Tobias-Huth/BinClock/pics/20241218_153026.jpg

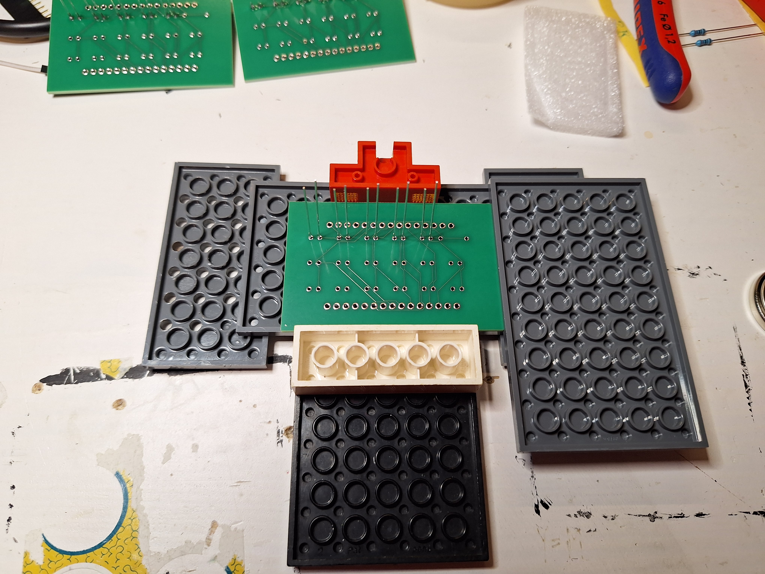
pics/20241218_153026.jpg
