Tobias-Huth/BinClock/pics/20241218_160921.jpg

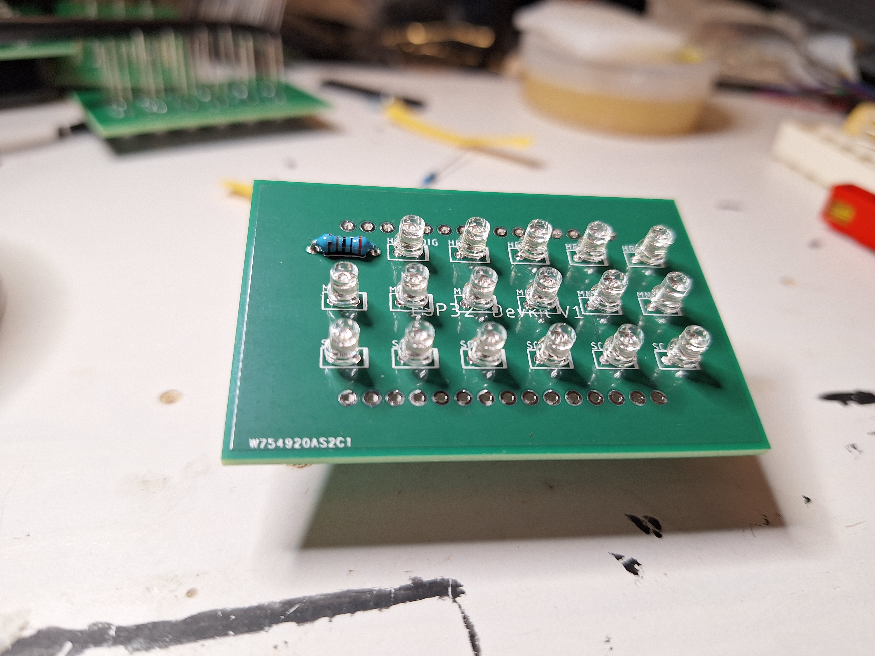
pics/20241218_160921.jpg
