Tobias-Huth/BinClock/pics/20241218_161102.jpg

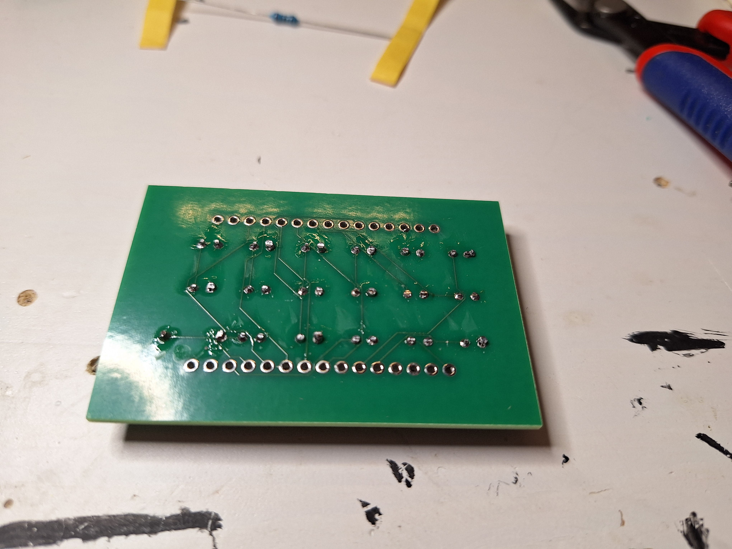
pics/20241218_161102.jpg
