Tobias-Huth/BinClock/pics/20241218_162006.jpg

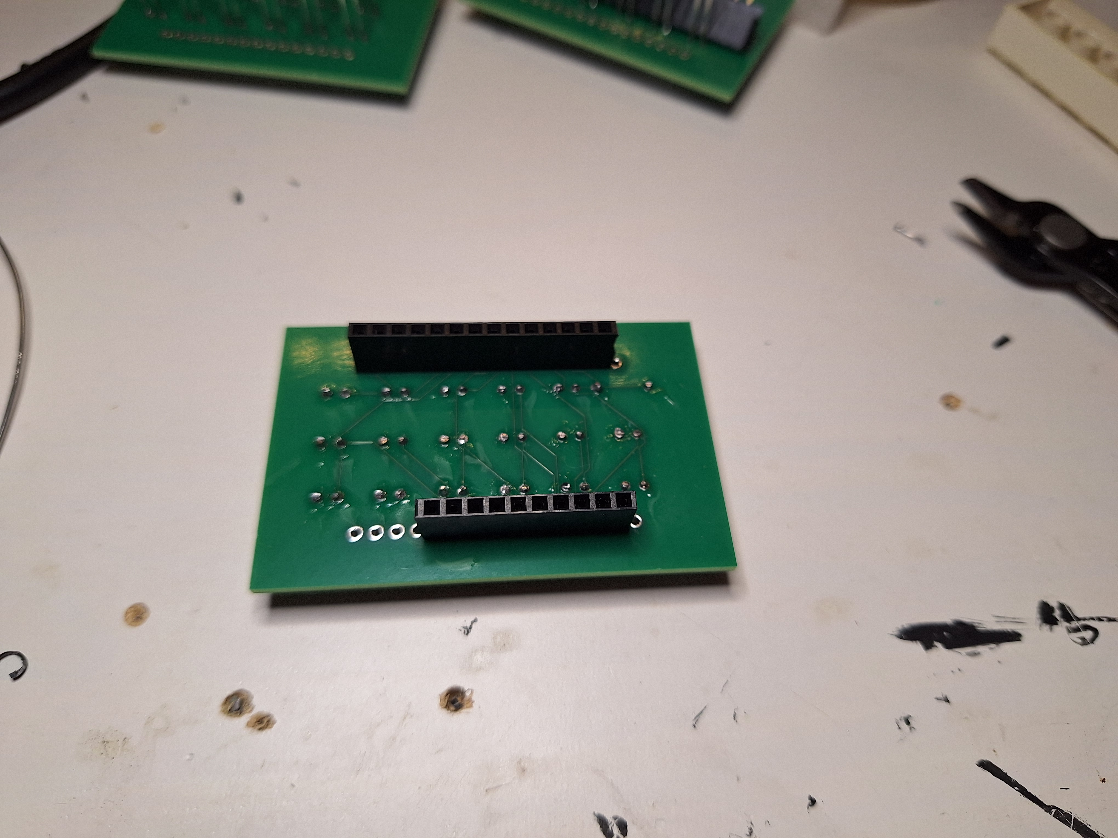
pics/20241218_162006.jpg
