Tobias-Huth/BinClock/pics/20241219_142211.jpg

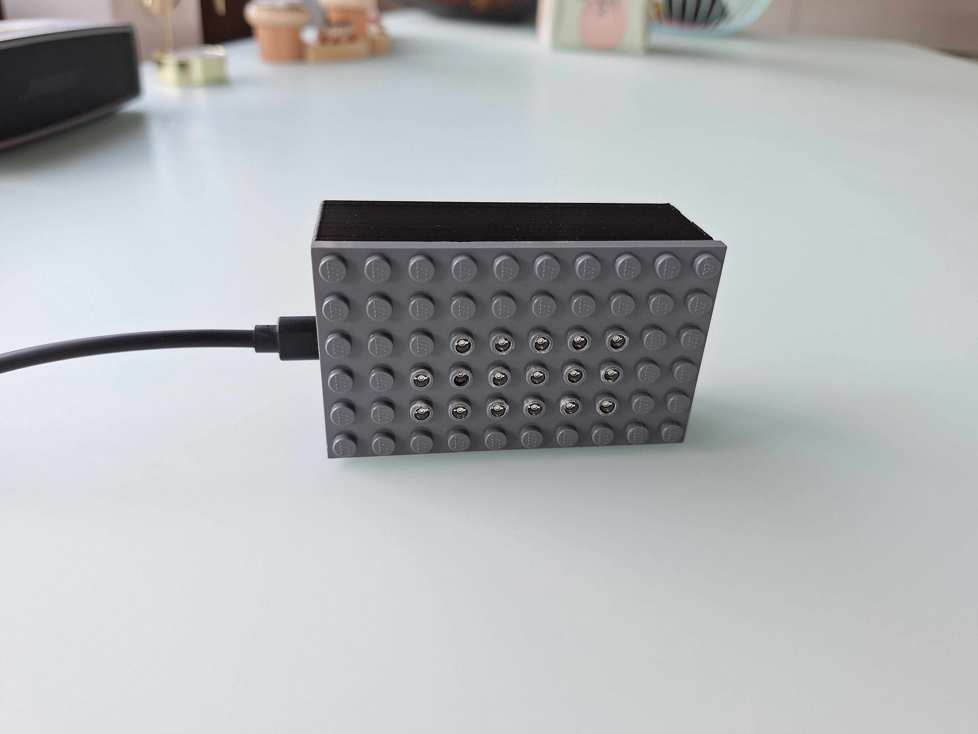
pics/20241219_142211.jpg
