Tobias-Huth/BinClock/pics/20241219_142215.jpg

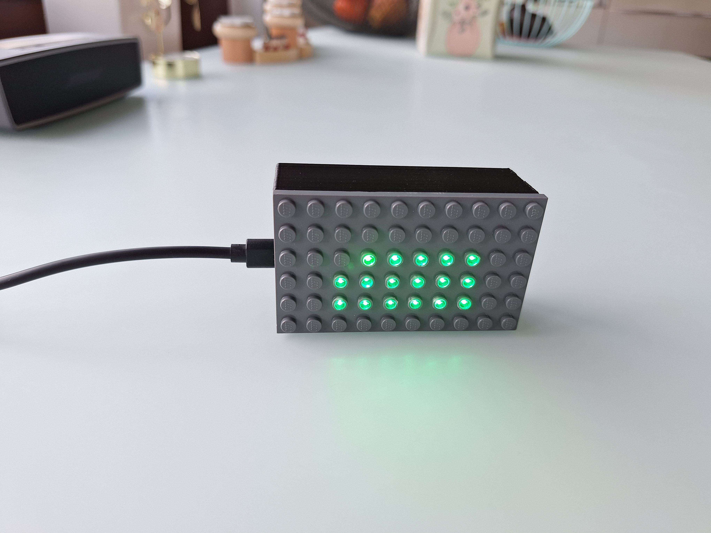
pics/20241219_142215.jpg
