Tobias-Huth/BinClock/pics/20241219_142327.jpg

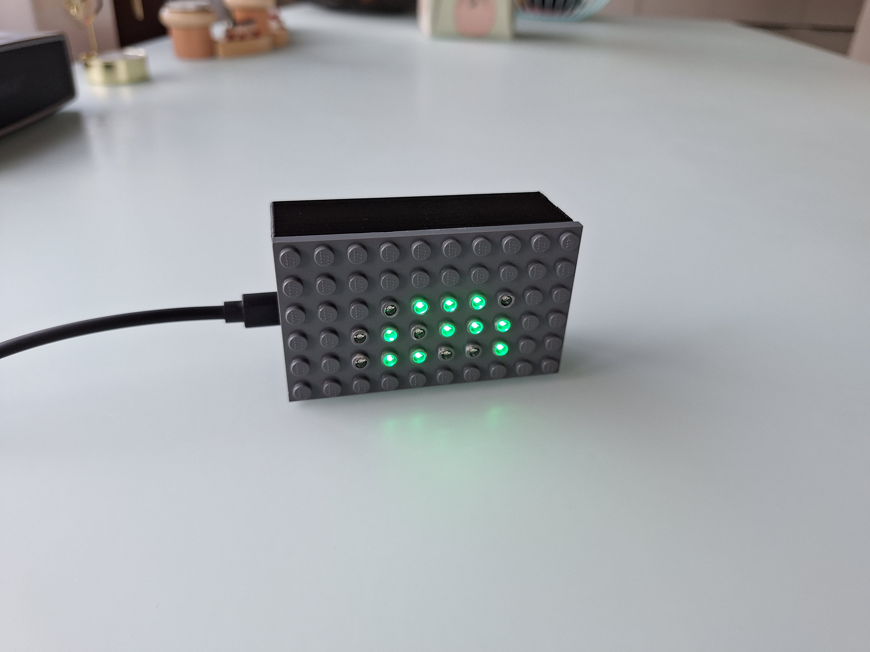
pics/20241219_142327.jpg
