Tobias-Huth/BinClock/pics/20241219_142519.jpg

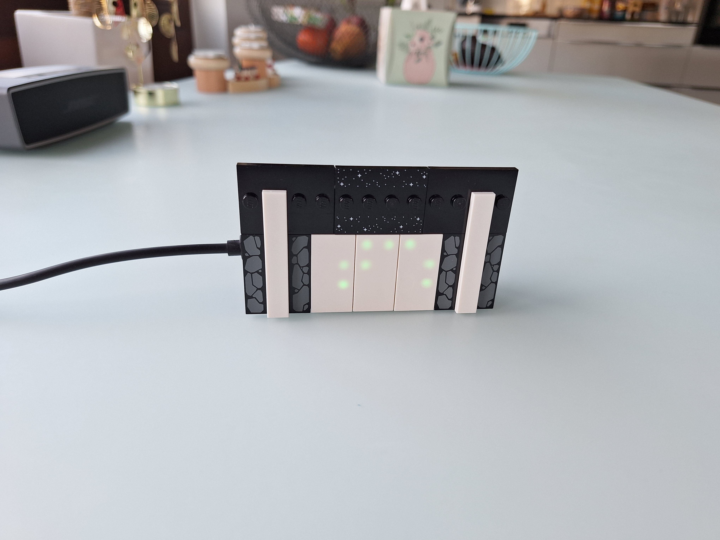
pics/20241219_142519.jpg
