Tobias-Huth/BinClock/pics/20241219_144131.jpg

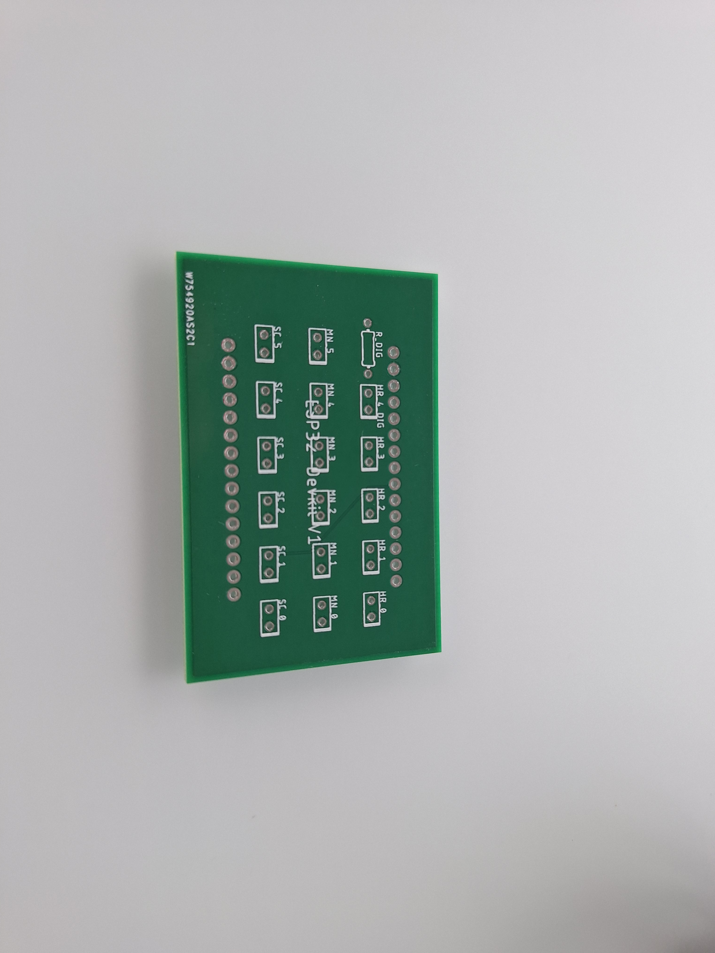
pics/20241219_144131.jpg
