Tobias-Huth/BinClock/pics/20241219_145637.jpg

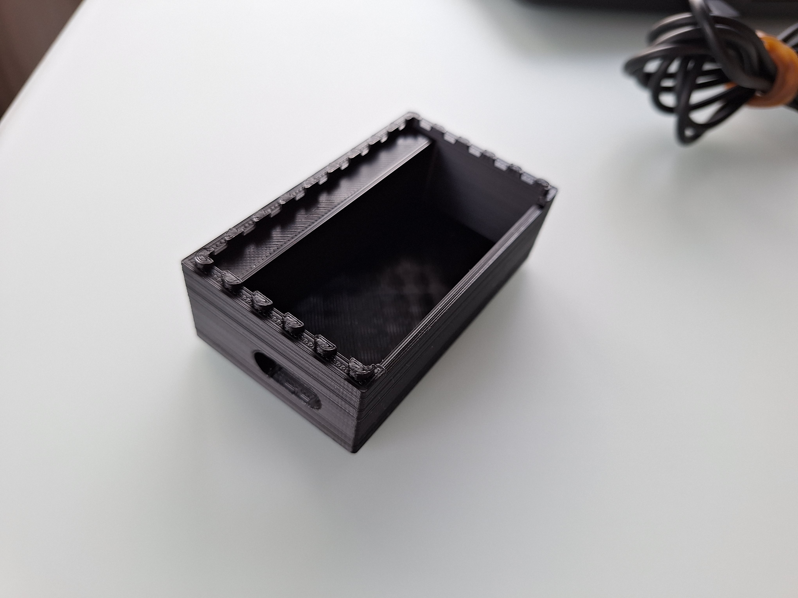
pics/20241219_145637.jpg
