Tobias-Huth/BinClock/BinClock_SW/ASCII_Table.h

const uint ASCII_table[96][3] = {
  { 00, 00, 00 },  // space  32
  { 00, 23, 00 },  // !      33
  { 03, 00, 03 },  // "      34
  { 10, 31, 10 },  // #      35
  { 23, 31, 29 },  // $      36
  { 25, 04, 19 },  // %      37
  { 22, 9, 20 },   // &      38
  { 00, 03, 00 },  // '      39
  { 14, 17, 00 },  // (      40
  { 00, 17, 14 },  // )      41
  { 05, 02, 05 },  // *      42
  { 04, 14, 04 },  // +      43
  { 00, 24, 00 },  // ,      44
  { 04, 04, 04 },  // -      45
  { 00, 16, 00 },  // .      46
  { 16, 14, 01 },  // /      47
  { 14, 17, 14 },  // 0      48
  { 02, 31, 00 },  // 1      49
  { 25, 21, 18 },  // 2      50
  { 17, 21, 10 },  // 3      51
  { 07, 04, 31 },  // 4      52
  { 23, 21, 29 },  // 5      53
  { 31, 21, 29 },  // 6      54
  { 01, 29, 03 },  // 7      55
  { 31, 21, 31 },  // 8      56
  { 23, 21, 31 },  // 9      57
  { 00, 10, 00 },  // :      58
  { 00, 26, 00 },  // ;      59
  { 04, 10, 17 },  // <      60
  { 20, 20, 20 },  // =      61
  { 17, 10, 04 },  // >      62
  { 01, 21, 03 },  // ?      63
  { 14, 21, 9 },   // @      64
  { 30, 05, 30 },  // A      65
  { 31, 21, 10 },  // B      66
  { 31, 17, 17 },  // C      67
  { 31, 17, 14 },  // D      68
  { 31, 21, 21 },  // E      69
  { 31, 05, 05 },  // F      70
  { 31, 17, 29 },  // G      71
  { 31, 04, 31 },  // H      72
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
  { 00, 00, 00 }   // DEL    127
};
